sharandac/powermeter/data/ACS712.jpg

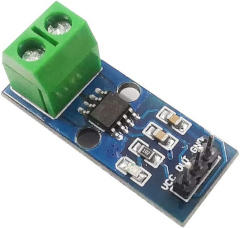
data/ACS712.jpg
