sharandac/powermeter/data/bad_sin.png

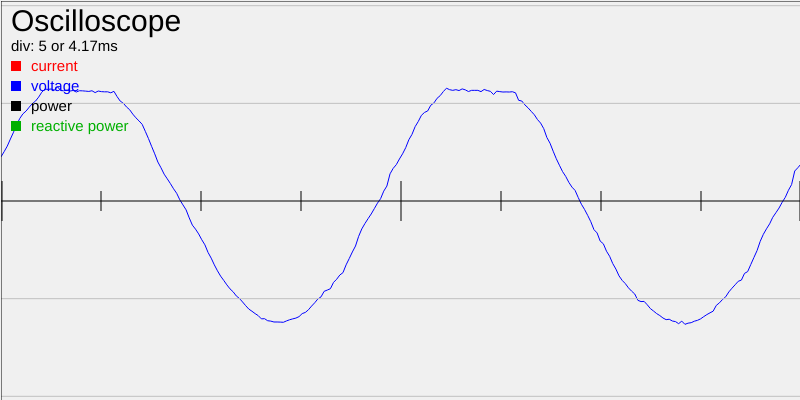
data/bad_sin.png
