sharandac/powermeter/data/good_sin.png

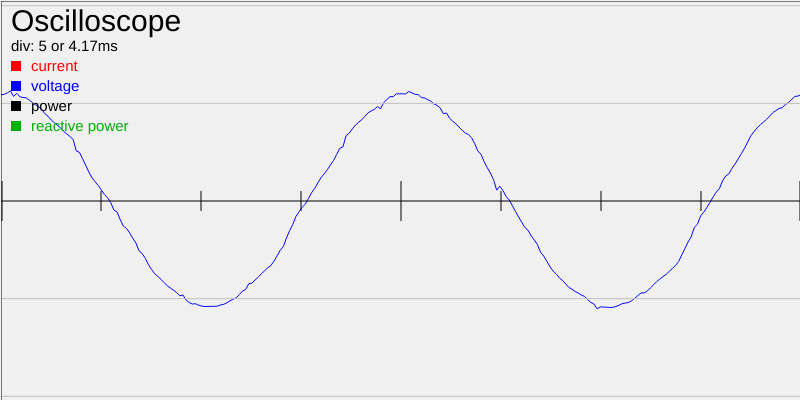
data/good_sin.png
