sharandac/powermeter/data/SCT013-000.jpg

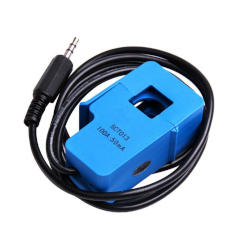
data/SCT013-000.jpg
