sharandac/powermeter/data/ZMPT101B.jpg

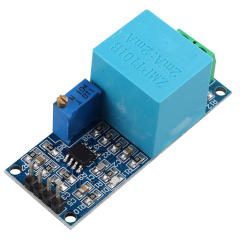
data/ZMPT101B.jpg
