sharandac/powermeter/images/live-view.png

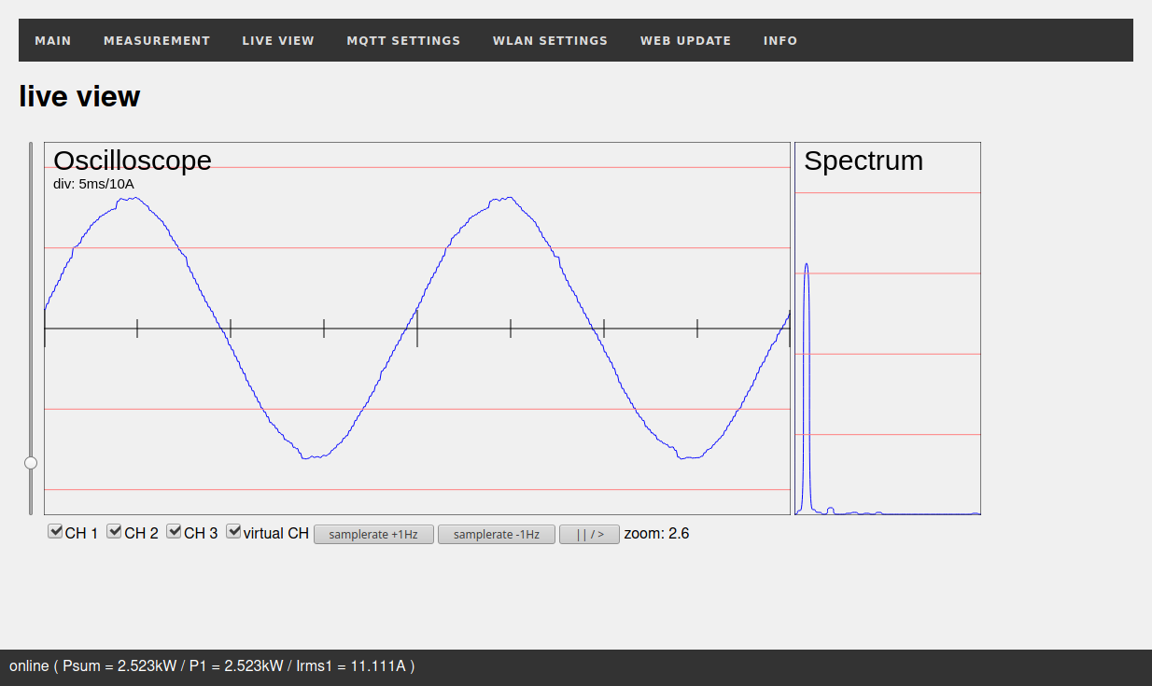
images/live-view.png
