sharandac/powermeter/images/SCT013-000.png

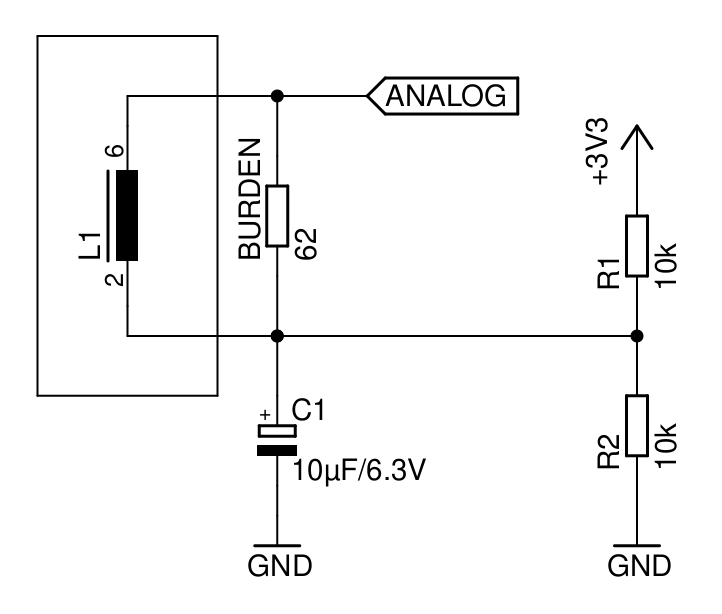
images/SCT013-000.png
